hmatuschek/sna/hardware/buffer.asc

C1: cap; 100n
C2: cap; 220nF
C3: cap; 220n
C4: cap; 100n
L1: ind; 100µ
Q1: npn; 2N3904
Q2: npn; 2N3904
R1: res; 1.2k
R2: res; 220
R3: res; 100
R4: res; 220
R5: res; 220
R6: res; 50
R7: res; 0.1
R8: res; 200
R9: res; 100
V1: voltage; SINE(0 4.5 40e6); AC 300m
V2: voltage; 4.6
Named nets: 0, DDS, OUT
.TRAN 1n 11u 10u
